vineethk96/CASA0014_Lumos/docs/PXL_20241202_111428234.jpg

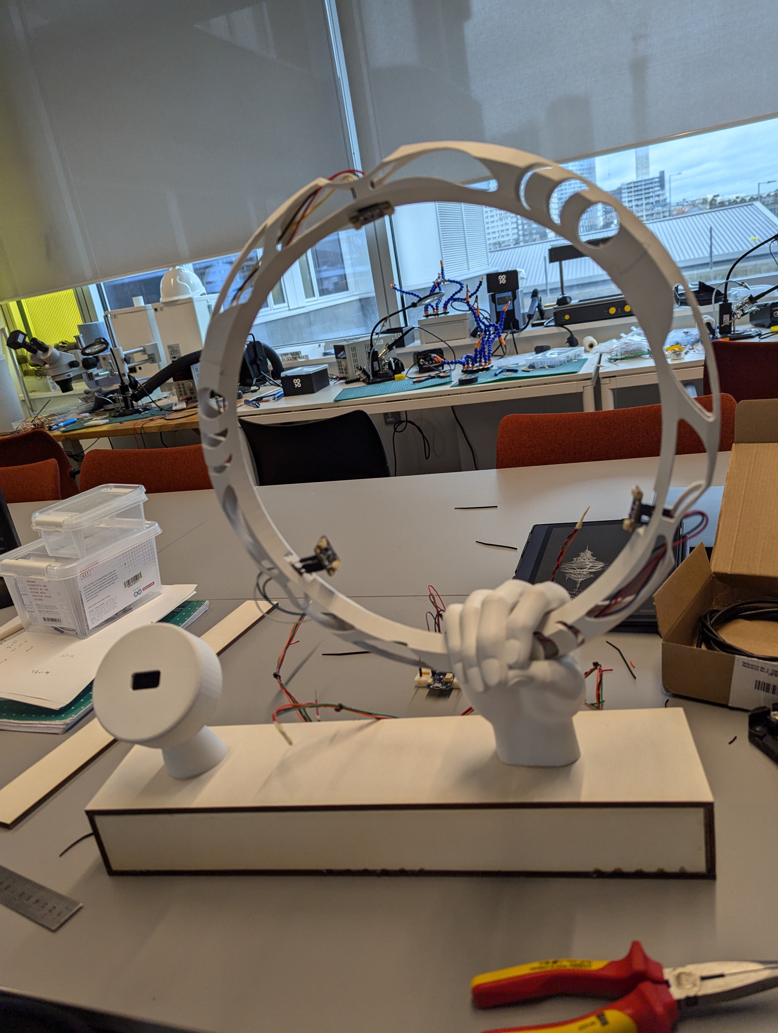
docs/PXL_20241202_111428234.jpg
