vineethk96/CASA0014_Lumos/docs/PXL_20241213_134007788.jpg

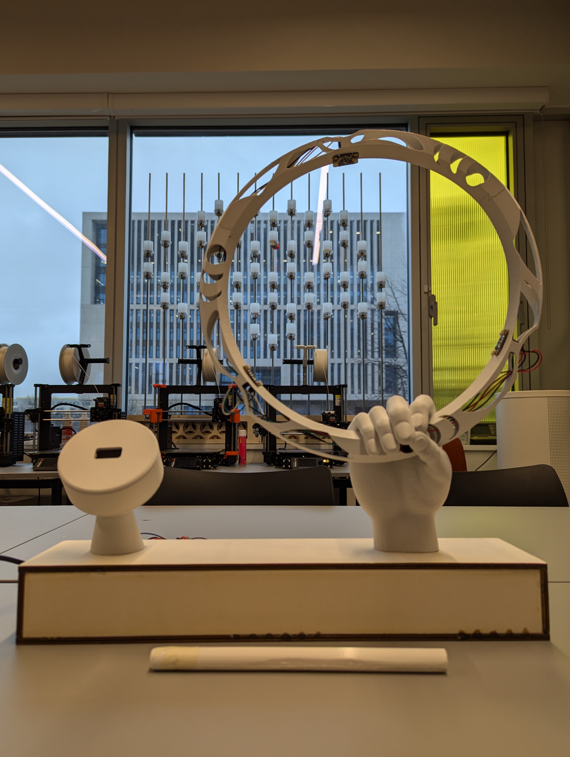
docs/PXL_20241213_134007788.jpg
