vineethk96/CASA0014_Lumos/docs/PXL_20241213_134013753.jpg

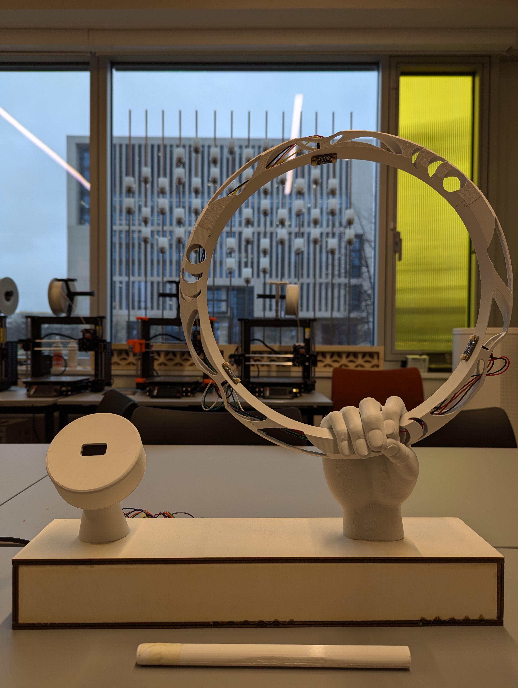
docs/PXL_20241213_134013753.jpg
