vineethk96/CASA0014_Lumos/docs/PXL_20241213_134041724.jpg

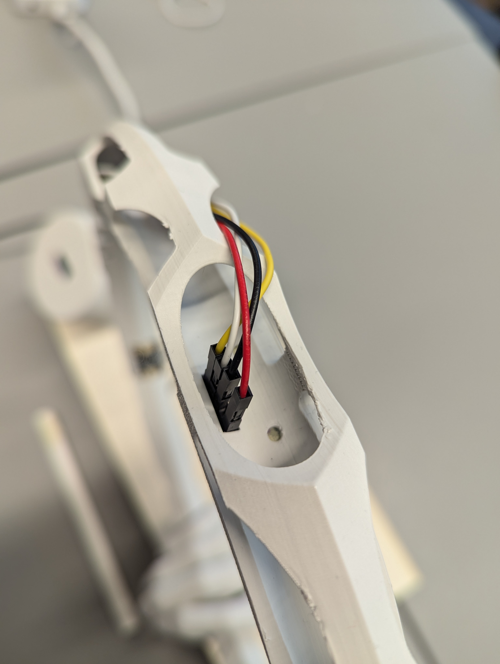
docs/PXL_20241213_134041724.jpg
