vineethk96/CASA0014_Lumos/docs/PXL_20241213_135521725.jpg

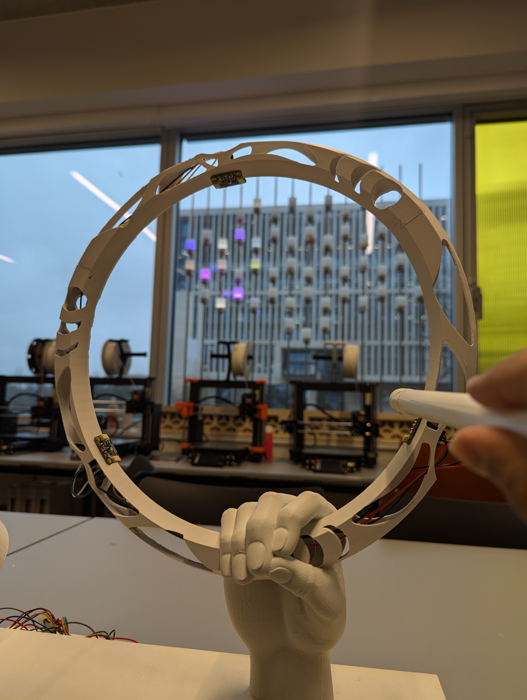
docs/PXL_20241213_135521725.jpg
