vineethk96/CASA0014_Lumos/docs/PXL_20241213_142637242.jpg

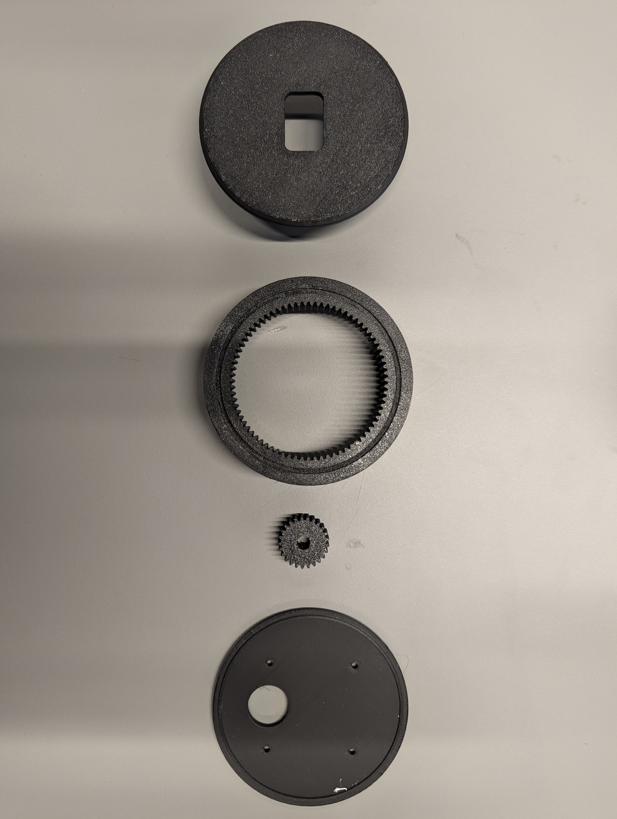
docs/PXL_20241213_142637242.jpg
