vineethk96/CASA0014_Lumos/docs/PXL_20241213_143206163.jpg

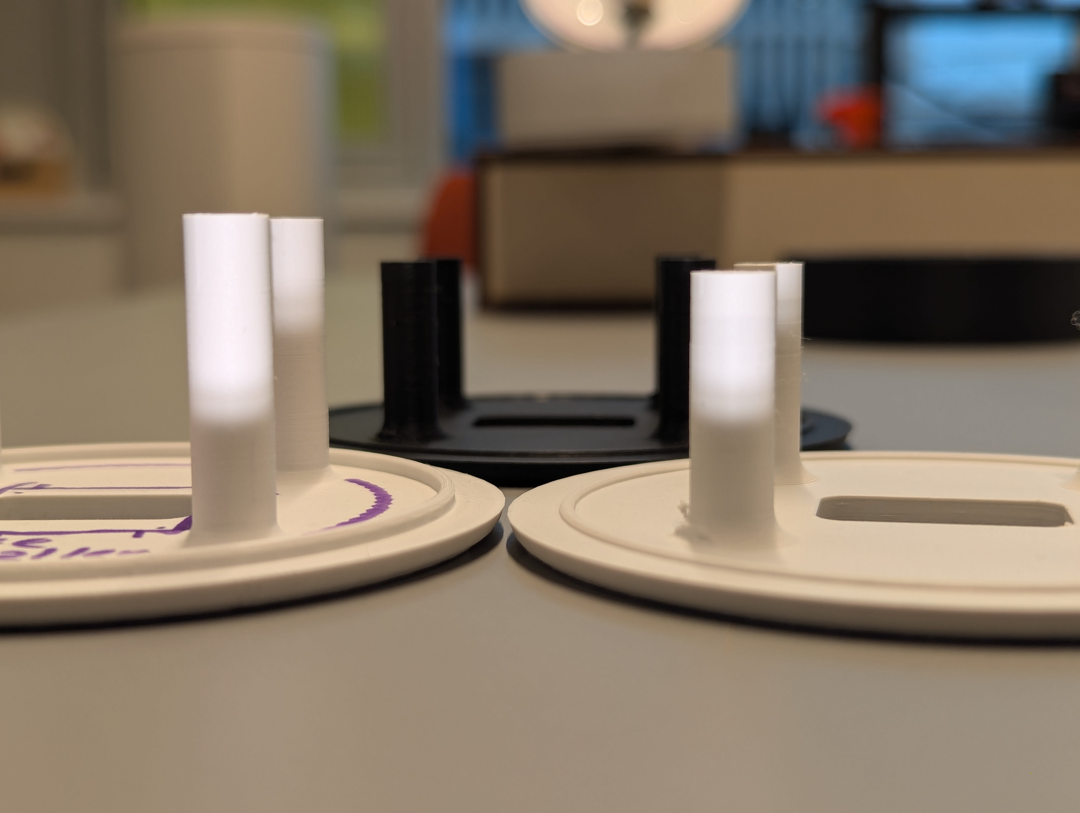
docs/PXL_20241213_143206163.jpg
