vineethk96/CASA0014_Lumos/docs/PXL_20241213_143935511.jpg

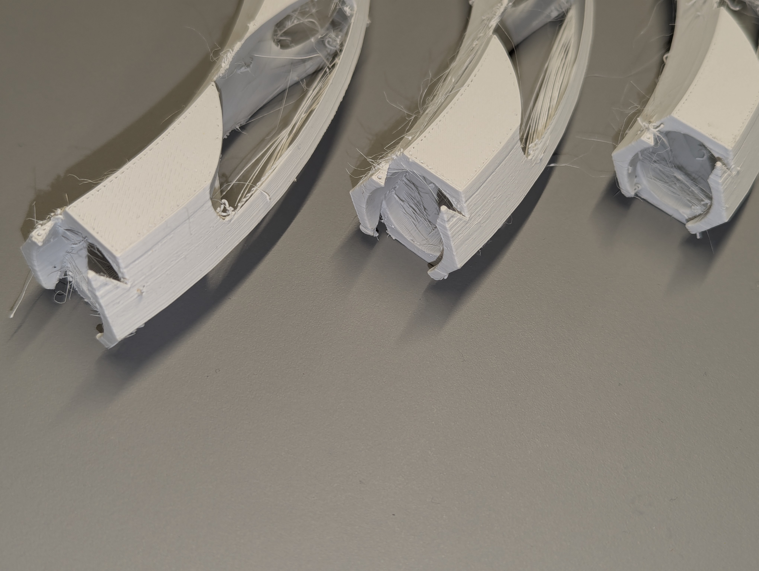
docs/PXL_20241213_143935511.jpg
