vineethk96/CASA0014_Lumos/docs/PXL_20241213_144031448.jpg

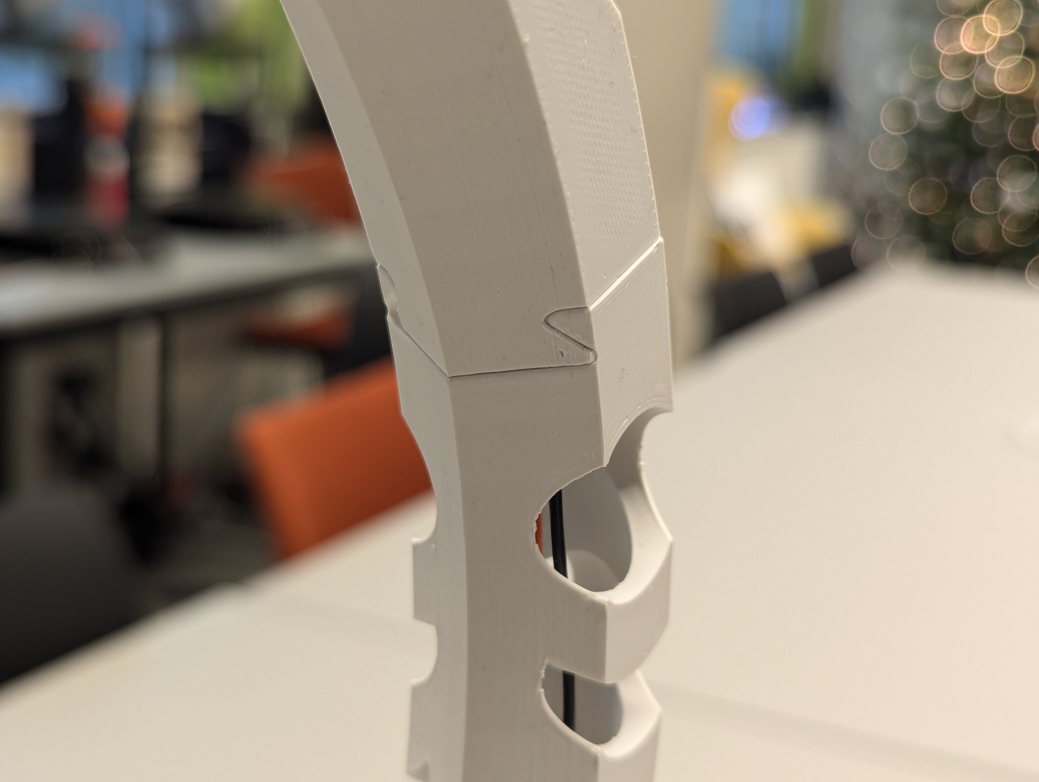
docs/PXL_20241213_144031448.jpg
