vineethk96/CASA0014_Lumos/docs/PXL_20241213_144142856.jpg

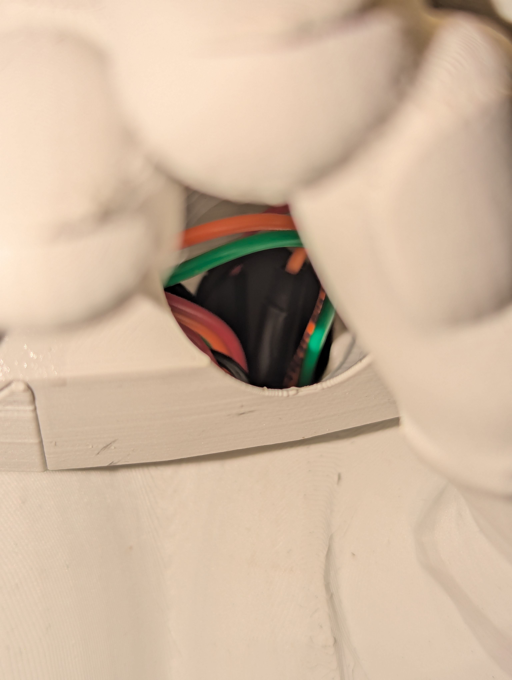
docs/PXL_20241213_144142856.jpg
