vineethk96/CASA0014_Lumos/docs/PXL_20241213_144335768.jpg

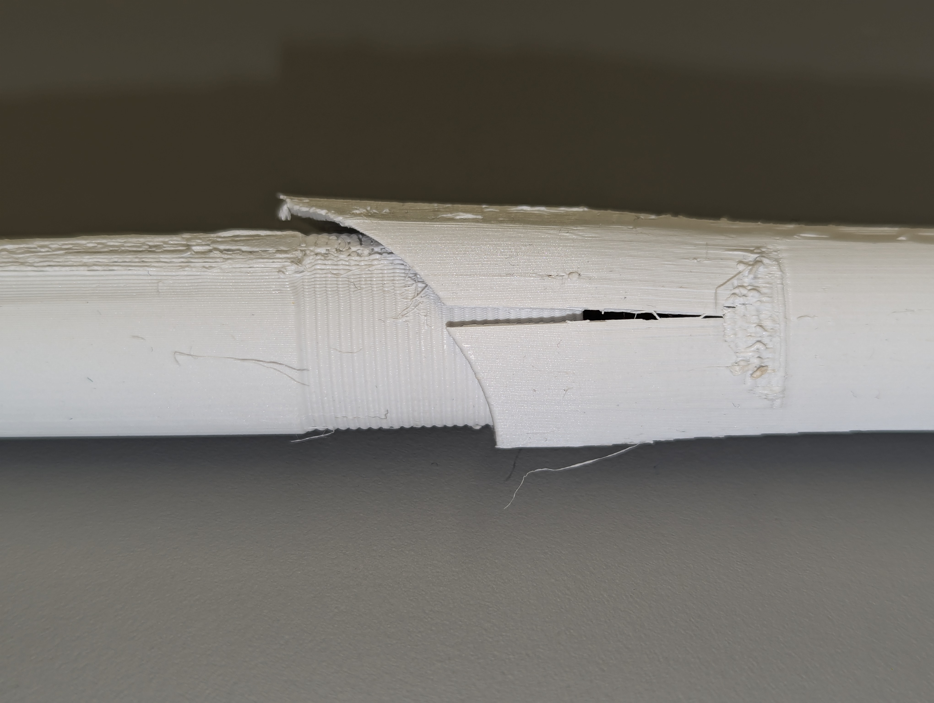
docs/PXL_20241213_144335768.jpg
