vineethk96/CASA0014_Lumos/docs/PXL_20241213_144436538.jpg

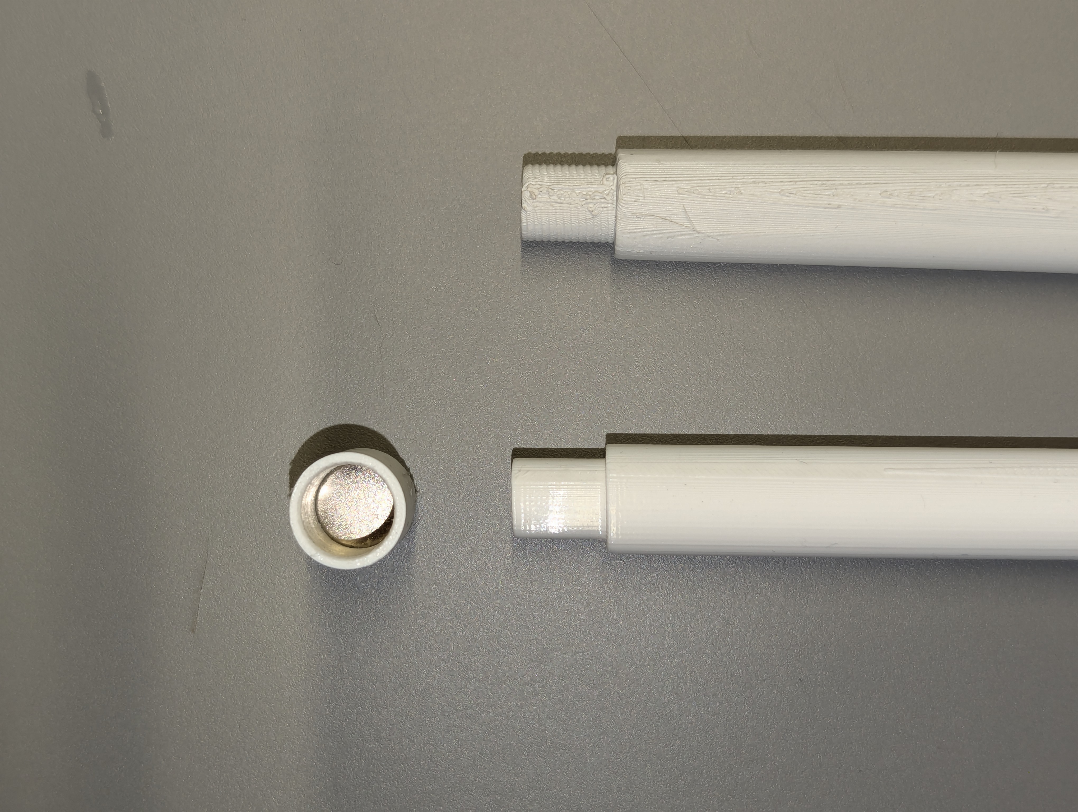
docs/PXL_20241213_144436538.jpg
