vineethk96/CASA0014_Lumos/cad/dial/v1.0/topPlate - Part 1.3mf

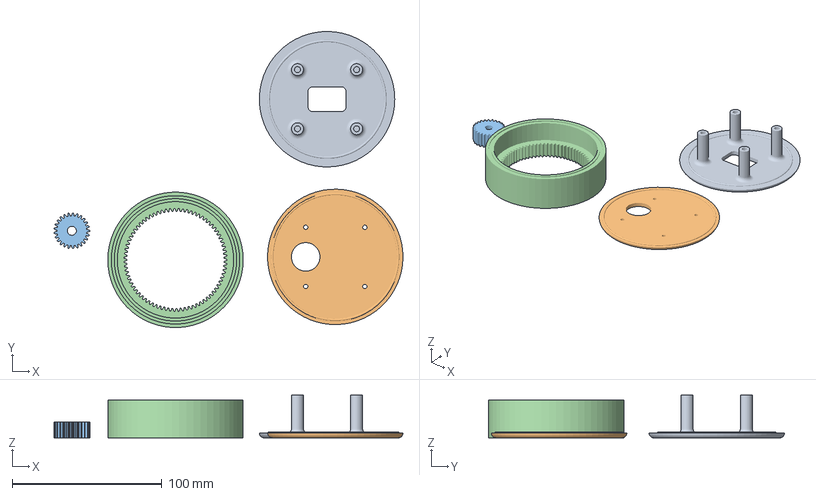
[picture p41: CAD file, 2025-01-04, an earlier design]
cad/dial/v1.0/topPlate - Part 1.3mf
233.2 x 197.7 x 28.6 mm
topPlate - Part 1.stl
basePlate - Part 1.stl
rotary_gear.stl
ring_gear.stl
