vineethk96/CASA0014_Lumos/cad/dial/v1.0/ring_gear.3mf

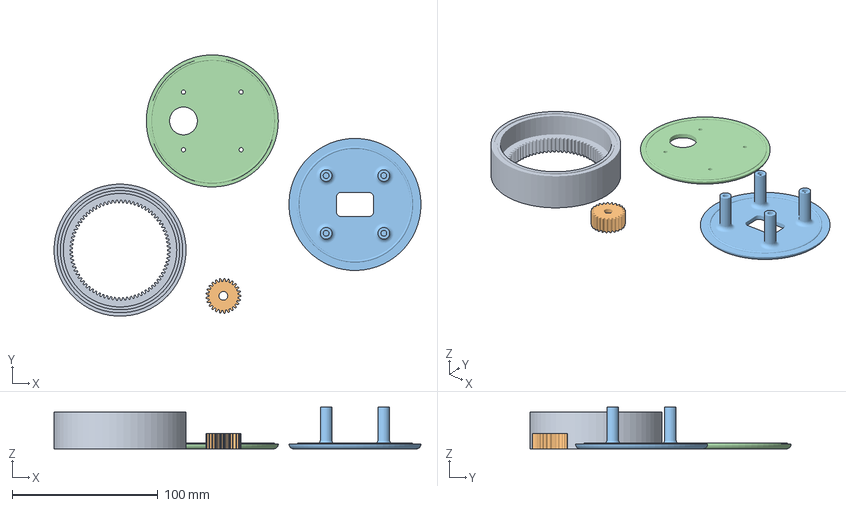
[picture p42: CAD file, 2025-01-04, an earlier design]
cad/dial/v1.0/ring_gear.3mf
251.4 x 178.9 x 28.6 mm
ring_gear.stl
rotary_gear.stl
topPlate - Part 1.stl
basePlate - Part 1.stl
